MOSH-Insa-Toulouse/2024-2025-4GP-Clara-Anatolie/Code Arduino/Codes_Arduino_Tests/clavier/clavier.ino

#define Left 8 // Left (X1) to digital pin 8
#define Bottom 9 // Bottom (Y2) to digital pin 9
#define Right 10 // Right (X2) to digital pin 10
#define Top 11 // Top (Y1) to digital pin 11

// Analog connections
#define topInput 0 // Top (Y1) to analog pin 0
#define rightInput 1 // Right (X2) to analog pin 1

int coordX = 0, coordY = 0;

void setup() {
 Serial.begin(38400); 
}

void loop() {
if (touch()) // If screen touched, print co-ordinates
{
//Serial.print(coordX);
//Serial.print(" ");
//Serial.println(coordY);
delay(250);

if ((coordX>100) && (coordX<230) && (coordY<850) && (coordY>640)) {Serial.println("1");}
if ((coordX>100) && (coordX<230) && (coordY<640) && (coordY>387)) {Serial.println("2");}
if ((coordX>100) && (coordX<230) && (coordY<387) && (coordY>130)) {Serial.println("3");}
if ((coordX>300) && (coordX<510) && (coordY<850) && (coordY>740)) {Serial.println("4");}
if ((coordX>300) && (coordX<510) && (coordY<640) && (coordY>387)) {Serial.println("5");}
if ((coordX>300) && (coordX<510) && (coordY<387) && (coordY>130)) {Serial.println("6");}
if ((coordX>510) && (coordX<720) && (coordY<850) && (coordY>640)) {Serial.println("7");}
if ((coordX>510) && (coordX<720) && (coordY<640) && (coordY>387)) {Serial.println("8");}
if ((coordX>510) && (coordX<720) && (coordY<387) && (coordY>130)) {Serial.println("9");}
if ((coordX>720) && (coordX<1000) && (coordY<850) && (coordY>740)) {Serial.println("C");}
if ((coordX>720) && (coordX<1000) && (coordY<640) && (coordY>387)) {Serial.println("0");}
if ((coordX>720) && (coordX<1000) && (coordY<387) && (coordY>130)) {Serial.println("E");}
}
}//fin du void

boolean touch() // return TRUE if touched, and set coordinates to touchX and touchY
{
boolean touch = false;
// get horizontal co-ordinates
pinMode(Left, OUTPUT);
digitalWrite(Left, LOW); // Set Left to Gnd
pinMode(Right, OUTPUT); // Set right to +5v
digitalWrite(Right, HIGH);
pinMode(Top, INPUT); // Top and Bottom to high impedance
pinMode(Bottom, INPUT);
delay(3);
coordX = analogRead(topInput);

// get vertical co-ordinates
pinMode(Bottom, OUTPUT); // set Bottom to Gnd
digitalWrite(Bottom, LOW);
pinMode(Top, OUTPUT); // set Top to +5v
digitalWrite(Top, HIGH);
pinMode(Right, INPUT); // left and right to high impedance
pinMode(Left, INPUT);
delay(3);
coordY = analogRead(rightInput);
// if co-ordinates read are less than 1000 and greater than 0 then the screen has been touched
if(coordX < 1000 && coordX > 0 && coordY < 1000 && coordY > 0) {touch = true;}
return touch;
}
