MOSH-Insa-Toulouse/2024-2025-4GP-Clara-Anatolie/Code Arduino/Codes_Arduino_Tests/MsTimer2/mstimerrrrr/mstimerrrrr.ino

#include <MsTimer2.h> // inclusion de la librairie Timer2
const int LED=2; //declaration constante de broche 

void setup()   { // debut de la fonction setup()
pinMode(LED, OUTPUT); //met la broche en sortie 
// initialisation interruption Timer 2
  MsTimer2::set(1000, InterruptTimer2); // période 1000ms 
  MsTimer2::start(); // active Timer 2 
} // fin de la fonction setup()

void loop(){ // debut de la fonction loop()
}

//*************** Autres Fonctions du programme *************
void InterruptTimer2() { // beginning of the function interruption Timer2
  digitalWrite(LED, HIGH);
  delayMicroseconds(10000); // delayMicroseconds doesn’t block the interrupts
  digitalWrite(LED, LOW);
}
